TinyCircuits/TinyCircuits-TinyTV-ASK4002/images/TinyTV-bootloader-mode.jpg

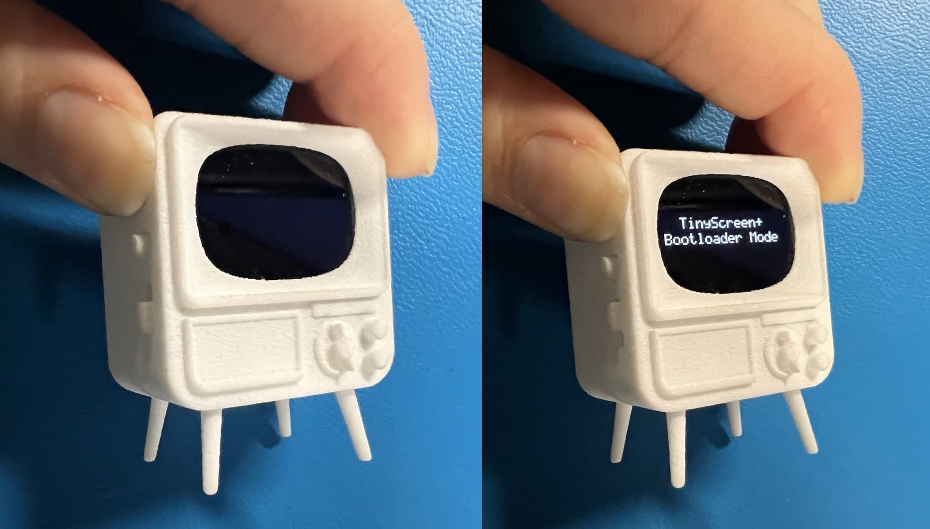
images/TinyTV-bootloader-mode.jpg
