TinyCircuits/TinyCircuits-TinyTV-ASK4002/images/TinyTV-Buttons.jpg

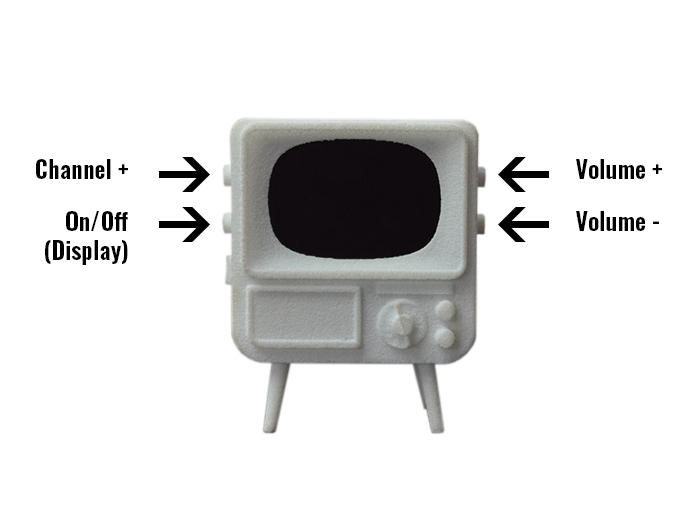
images/TinyTV-Buttons.jpg
