TinyCircuits/TinyCircuits-TinyTV-ASK4002/images/TinyTV-Custom-01.jpg

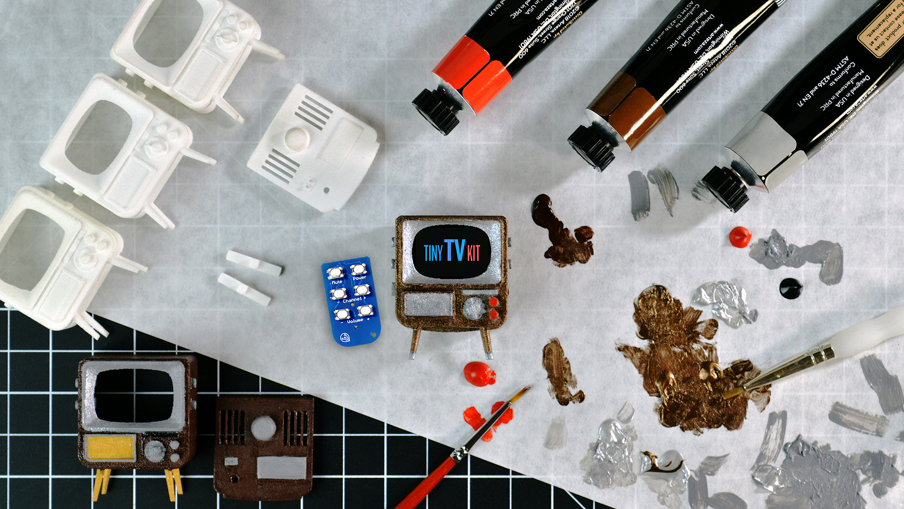
images/TinyTV-Custom-01.jpg
