TinyCircuits/TinyCircuits-TinyTV-ASK4002/images/TinyTV-Custom-02.gif

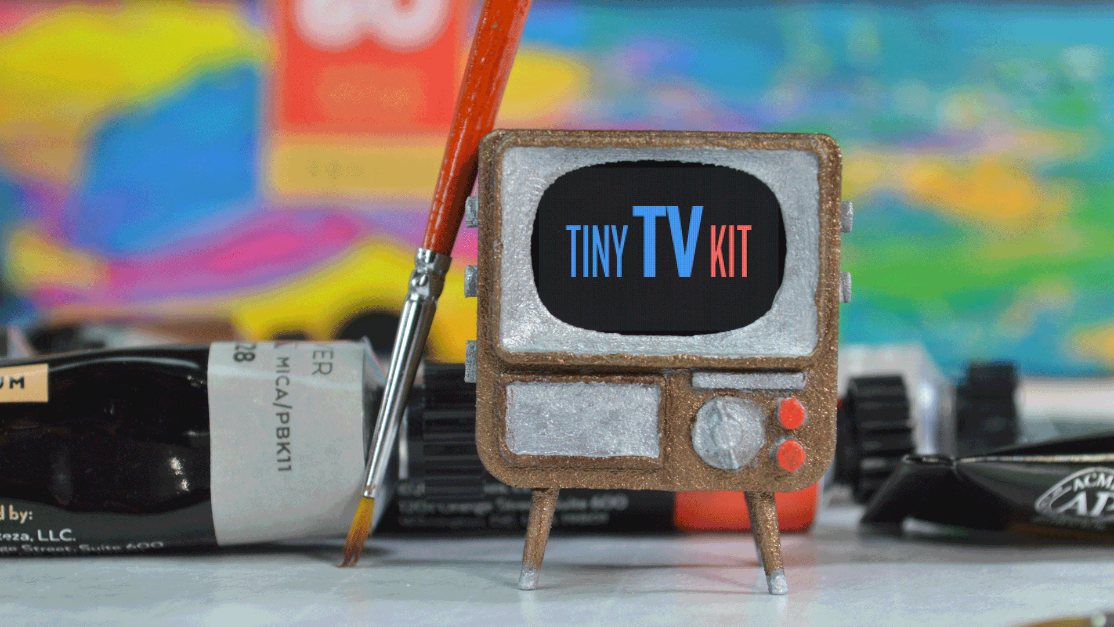
images/TinyTV-Custom-02.gif
