TinyCircuits/TinyCircuits-TinyTV-ASK4002/images/TinyTV-Custom-03.jpg

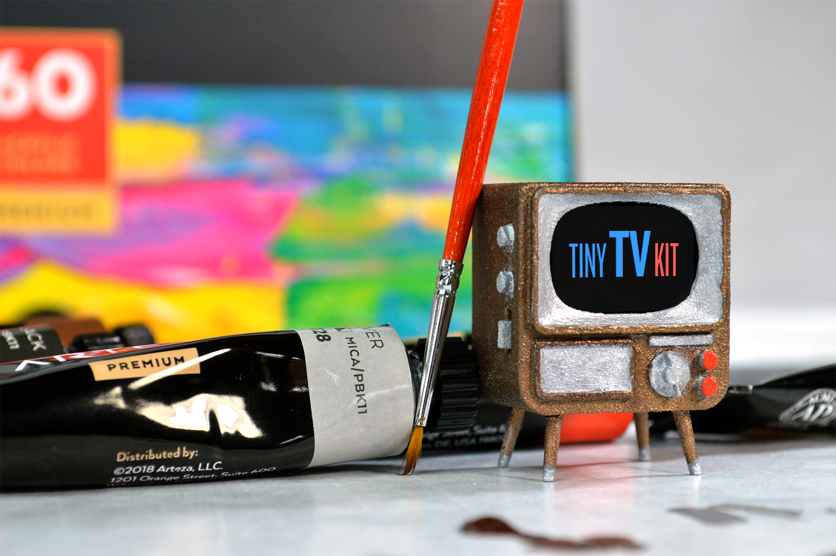
images/TinyTV-Custom-03.jpg
