TinyCircuits/TinyCircuits-TinyTV-ASK4002/images/TinyTV-Settings-Tutorial-Image-04.jpg

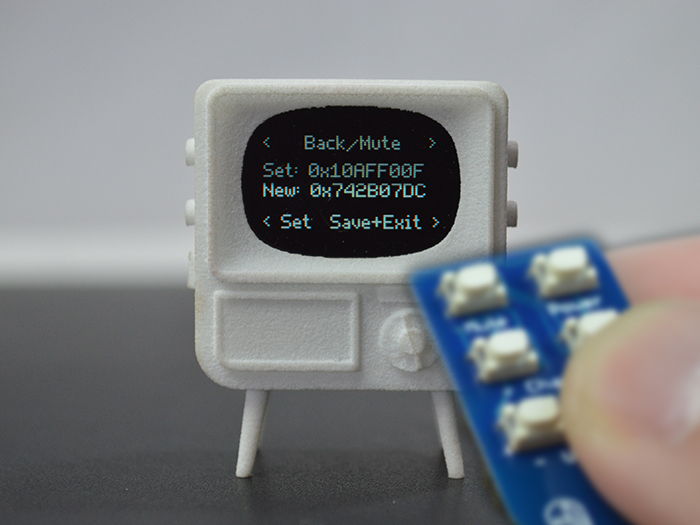
images/TinyTV-Settings-Tutorial-Image-04.jpg
