TinyCircuits/TinyCircuits-TinyTV-ASK4002/images/TinyTV-Tutorial-Image-02.png

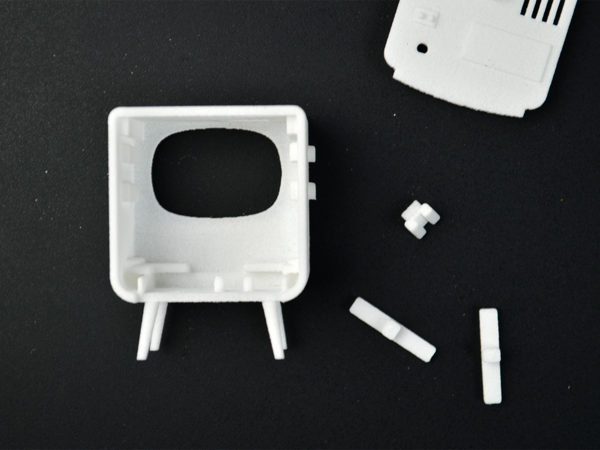
images/TinyTV-Tutorial-Image-02.png
