TinyCircuits/TinyCircuits-TinyTV-ASK4002/images/TinyTV-Tutorial-Image-04.png

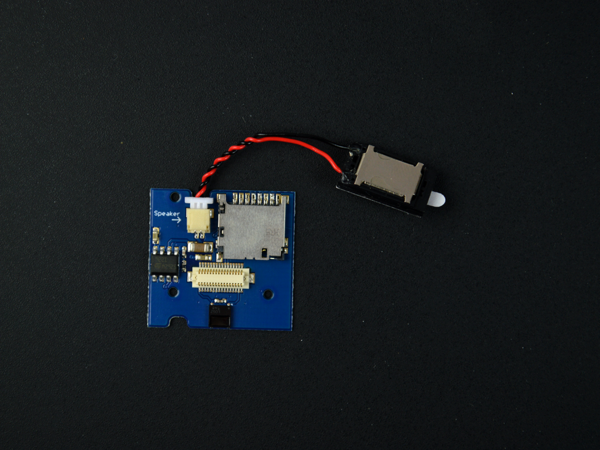
images/TinyTV-Tutorial-Image-04.png
