TinyCircuits/TinyCircuits-TinyTV-ASK4002/images/TinyTV-Tutorial-Image-05.png

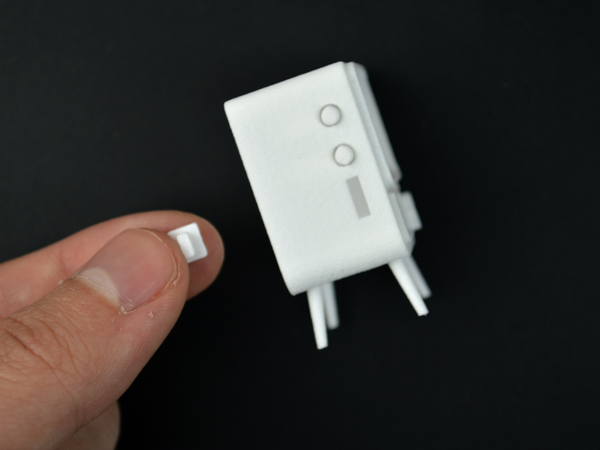
images/TinyTV-Tutorial-Image-05.png
