TinyCircuits/TinyCircuits-TinyTV-ASK4002/images/TinyTV-Tutorial-Image-07.png

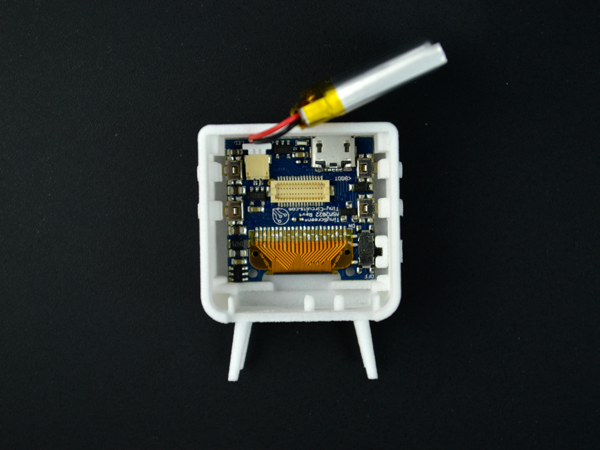
images/TinyTV-Tutorial-Image-07.png
