TinyCircuits/TinyCircuits-TinyTV-ASK4002/images/TinyTV-Tutorial-Image-08.png

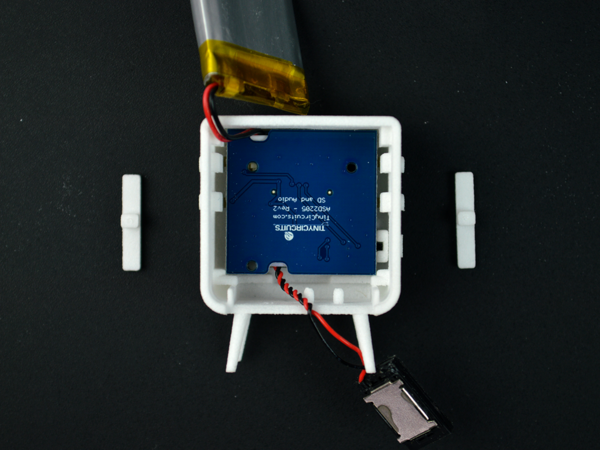
images/TinyTV-Tutorial-Image-08.png
