TinyCircuits/TinyCircuits-TinyTV-ASK4002/images/TinyTV-Tutorial-Image-09.png

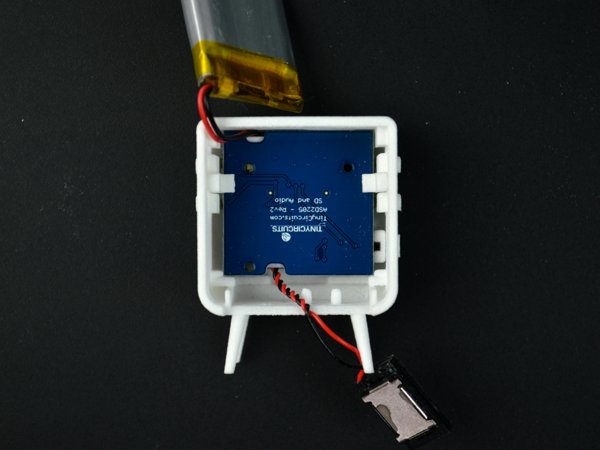
images/TinyTV-Tutorial-Image-09.png
