TinyCircuits/TinyCircuits-TinyTV-ASK4002/images/TinyTV-Tutorial-Image-11.png

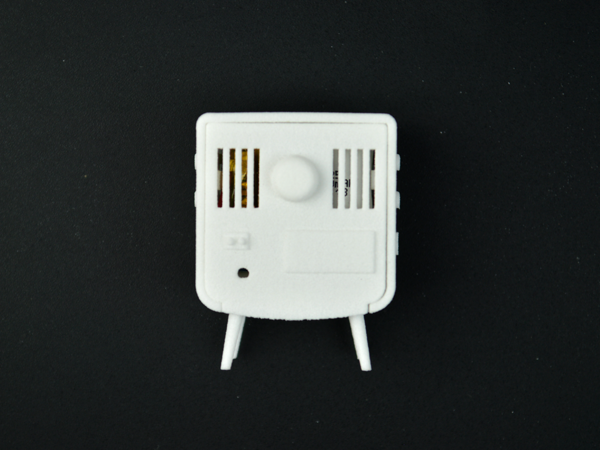
images/TinyTV-Tutorial-Image-11.png
