TinyCircuits/TinyCircuits-TinyTV-ASK4002/images/TinyTV-Tutorial-Image-13.png

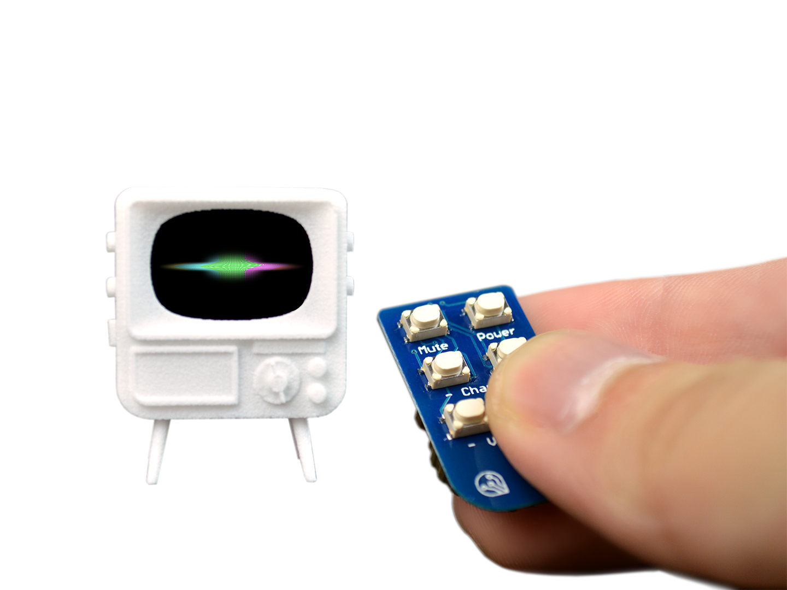
images/TinyTV-Tutorial-Image-13.png
