TinyCircuits/TinyCircuits-TinyTV-ASK4002/images/TinyTV_assembly-Image-10.png

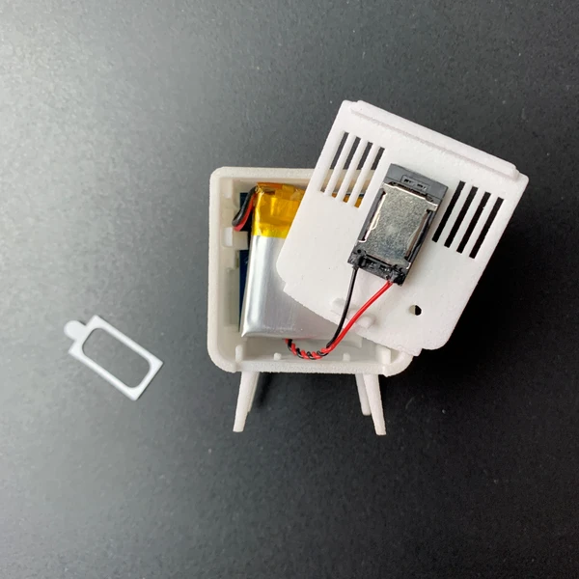
images/TinyTV_assembly-Image-10.png
