TinyCircuits/TinyCircuits-TinyTV-ASK4002/examples/Tiny-Video-Player/SdFat.cpp

/* Arduino SdFat Library
 * Copyright (C) 2012 by William Greiman
 *
 * This file is part of the Arduino SdFat Library
 *
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
 * You should have received a copy of the GNU General Public License
 * along with the Arduino SdFat Library.  If not, see
 * <http://www.gnu.org/licenses/>.
 */
#include "SdFat.h"
//------------------------------------------------------------------------------
void SdFatBase::errorHalt(Print* pr) {
  errorPrint(pr);
  while (1) {}
}
//------------------------------------------------------------------------------
void SdFatBase::errorHalt(Print* pr, char const* msg) {
  errorPrint(pr, msg);
  while (1) {}
}
//------------------------------------------------------------------------------
void SdFatBase::errorHalt(Print* pr, const __FlashStringHelper* msg) {
  errorPrint(pr, msg);
  while (1) {}
}
//------------------------------------------------------------------------------
void SdFatBase::errorPrint(Print* pr) {
  if (!cardErrorCode()) {
    return;
  }
  pr->print(F("SD errorCode: 0X"));
  pr->print(cardErrorCode(), HEX);
  pr->print(F(",0X"));
  pr->println(cardErrorData(), HEX);
}
//------------------------------------------------------------------------------
void SdFatBase::errorPrint(Print* pr, char const* msg) {
  pr->print(F("error: "));
  pr->println(msg);
  errorPrint(pr);
}
//------------------------------------------------------------------------------
void SdFatBase::errorPrint(Print* pr, const __FlashStringHelper* msg) {
  pr->print(F("error: "));
  pr->println(msg);
  errorPrint(pr);
}
//------------------------------------------------------------------------------
void SdFatBase::initErrorHalt(Print* pr) {
  initErrorPrint(pr);
  while (1) {}
}
//------------------------------------------------------------------------------
void SdFatBase::initErrorHalt(Print* pr, char const *msg) {
  pr->println(msg);
  initErrorHalt(pr);
}
//------------------------------------------------------------------------------
void SdFatBase::initErrorHalt(Print* pr, const __FlashStringHelper* msg) {
  pr->println(msg);
  initErrorHalt(pr);
}
//------------------------------------------------------------------------------
void SdFatBase::initErrorPrint(Print* pr) {
  if (cardErrorCode()) {
    pr->println(F("Can't access SD card. Do not reformat."));
    if (cardErrorCode() == SD_CARD_ERROR_CMD0) {
      pr->println(F("No card, wrong chip select pin, or SPI problem?"));
    }
    errorPrint(pr);
  } else if (vol()->fatType() == 0) {
    pr->println(F("Invalid format, reformat SD."));
  } else if (!vwd()->isOpen()) {
    pr->println(F("Can't open root directory."));
  } else {
    pr->println(F("No error found."));
  }
}
//------------------------------------------------------------------------------
void SdFatBase::initErrorPrint(Print* pr, char const *msg) {
  pr->println(msg);
  initErrorPrint(pr);
}
//------------------------------------------------------------------------------
void SdFatBase::initErrorPrint(Print* pr, const __FlashStringHelper* msg) {
  pr->println(msg);
  initErrorPrint(pr);
}
