TinyCircuits/TinyCircuits-TinyTV-ASK4002/examples/Tiny-Video-Player/audio.ino

void tcConfigure(uint32_t sampleRate)
{
  // Enable GCLK for TCC2 and TC5 (timer counter input clock)
  GCLK->CLKCTRL.reg = (uint16_t) (GCLK_CLKCTRL_CLKEN | GCLK_CLKCTRL_GEN_GCLK0 | GCLK_CLKCTRL_ID(GCM_TC4_TC5)) ;
  while (GCLK->STATUS.bit.SYNCBUSY);

  tcReset();

  // Set Timer counter Mode to 16 bits
  TC5->COUNT16.CTRLA.reg |= TC_CTRLA_MODE_COUNT16;

  // Set TC5 mode as match frequency
  TC5->COUNT16.CTRLA.reg |= TC_CTRLA_WAVEGEN_MFRQ;

  TC5->COUNT16.CTRLA.reg |= TC_CTRLA_PRESCALER_DIV1;

  TC5->COUNT16.CC[0].reg = (uint16_t) (SystemCoreClock / sampleRate - 1);
  while (tcIsSyncing());

  // Configure interrupt request
  NVIC_DisableIRQ(TC5_IRQn);
  NVIC_ClearPendingIRQ(TC5_IRQn);
  NVIC_SetPriority(TC5_IRQn, 0);
  NVIC_EnableIRQ(TC5_IRQn);

  // Enable the TC5 interrupt request
  TC5->COUNT16.INTENSET.bit.MC0 = 1;
  while (tcIsSyncing());
}


bool tcIsSyncing()
{
  return TC5->COUNT16.STATUS.reg & TC_STATUS_SYNCBUSY;
}

void tcStartCounter()
{
  // Enable TC

  TC5->COUNT16.CTRLA.reg |= TC_CTRLA_ENABLE;
  while (tcIsSyncing());
}

void tcReset()
{
  // Reset TCx
  TC5->COUNT16.CTRLA.reg = TC_CTRLA_SWRST;
  while (tcIsSyncing());
  while (TC5->COUNT16.CTRLA.bit.SWRST);
}

void tcDisable()
{
  // Disable TC5
  TC5->COUNT16.CTRLA.reg &= ~TC_CTRLA_ENABLE;
  while (tcIsSyncing());
}


#ifdef __cplusplus
extern "C" {
#endif

extern void Audio_Handler (void);
int dacOut;
void Audio_Handler (void)
{
  while (DAC->STATUS.bit.SYNCBUSY == 1);
  if(currentAudioBuffer==1){
    dacOut = audioBuffer1[sampleIndex++];
  }else{
    dacOut = audioBuffer2[sampleIndex++];
  }
  dacOut -= 511;
  dacOut = dacOut >> (maxVolume - volume);
  dacOut += 511;
  DAC->DATA.reg =  dacOut;
  while (DAC->STATUS.bit.SYNCBUSY == 1);

  if (sampleIndex > 1023 ){
    sampleIndex = 0;
    if(currentAudioBuffer==1){
      currentAudioBuffer=2;
    }else{
      currentAudioBuffer=1;
    }
  }

  // Clear the interrupt
  TC5->COUNT16.INTFLAG.bit.MC0 = 1;
}

void TC5_Handler (void) __attribute__ ((weak, alias("Audio_Handler")));

#ifdef __cplusplus
}
#endif
